sneakylizard123-4/PMM-1.0-R1/datasheets/simulations/TPS61089/amCharts (17).png

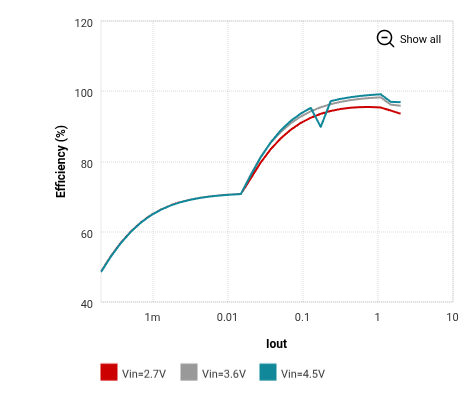
datasheets/simulations/TPS61089/amCharts (17).png
